thanhtuan2503/ControlBoard/documents/label.png

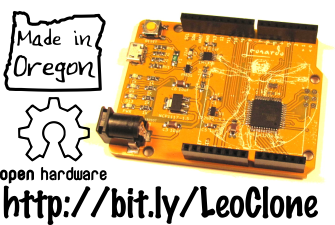
documents/label.png
