thanhtuan2503/ControlBoard/images/IMG_0759.JPG

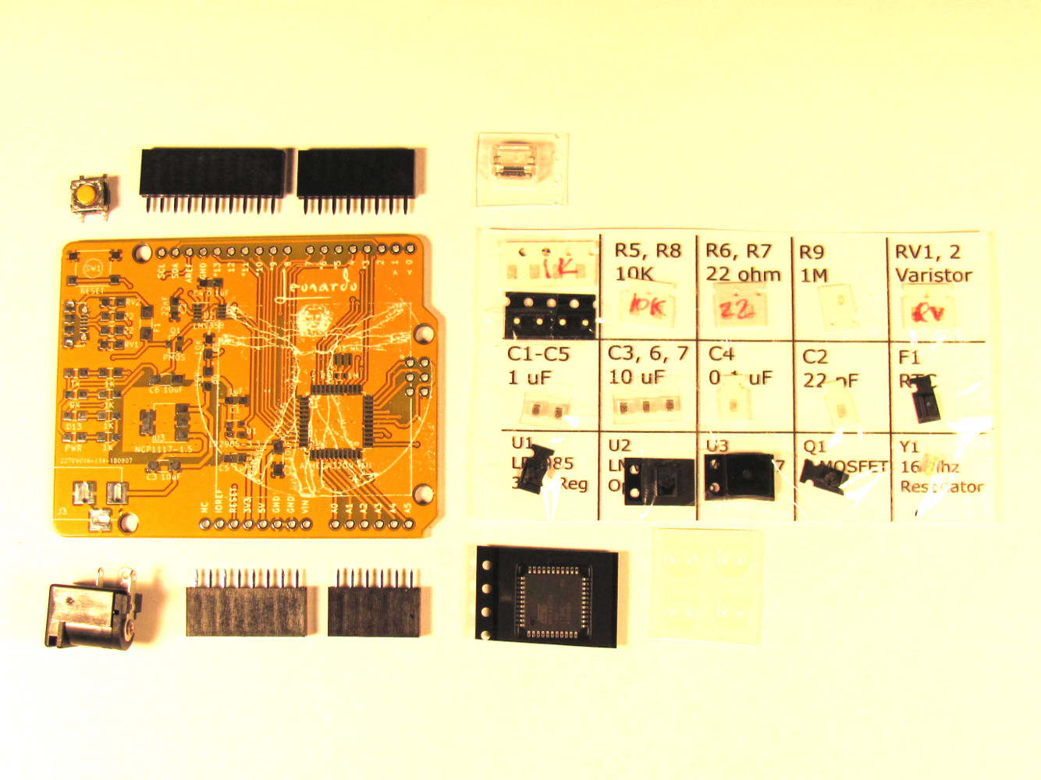
images/IMG_0759.JPG
