thanhtuan2503/ControlBoard/documents/parts.png

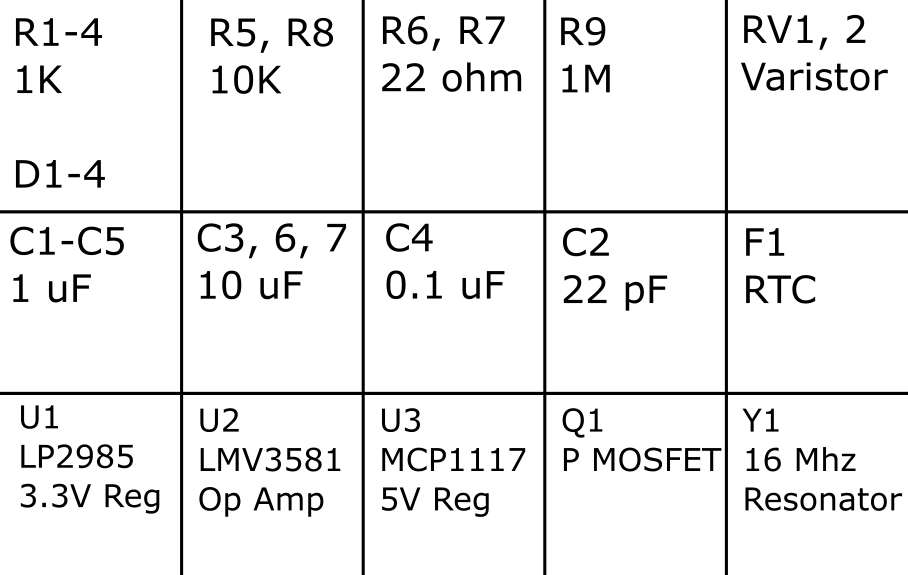
documents/parts.png
